mike-d3v/slime-stuff/dock/Plug.stl

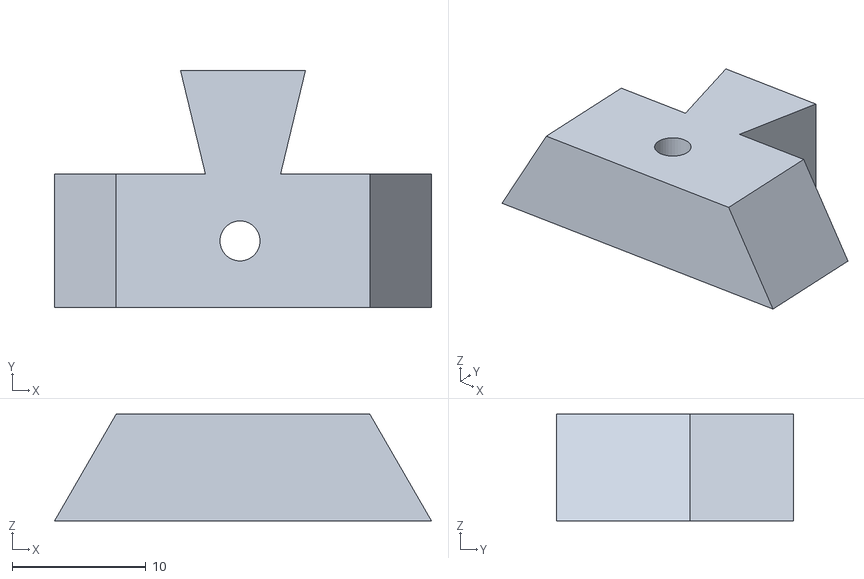
[picture p23: CAD file, 2022-05-23]
dock/Plug.stl
28.2 x 17.8 x 8.00
