mike-d3v/slime-stuff/buckles/secondary.stl

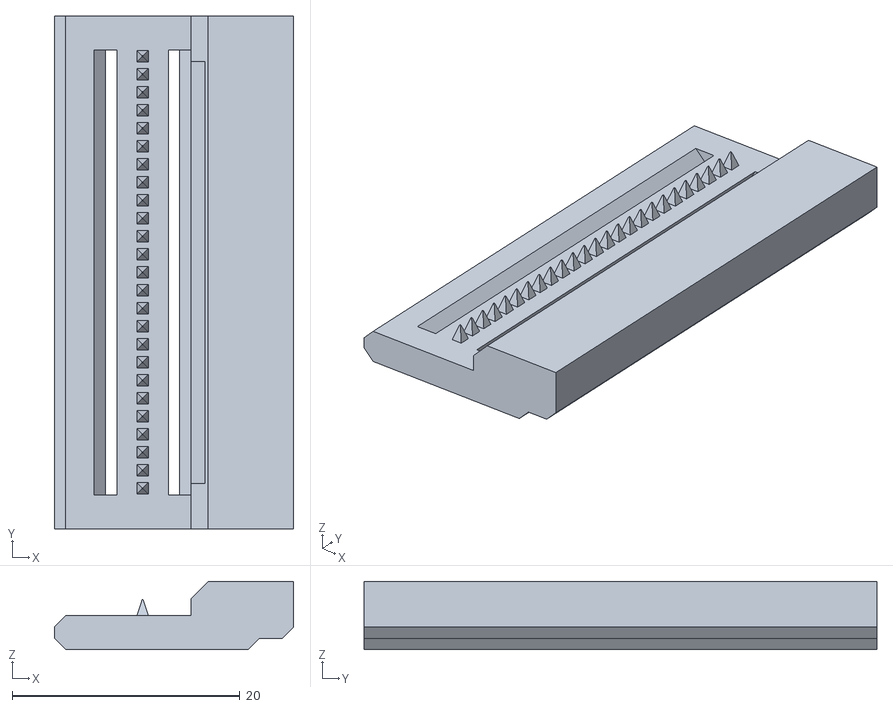
[picture p24: CAD file, 2022-05-23]
buckles/secondary.stl
21.0 x 45.0 x 6.00
