mike-d3v/slime-stuff/buckles/primaryExtension.stl

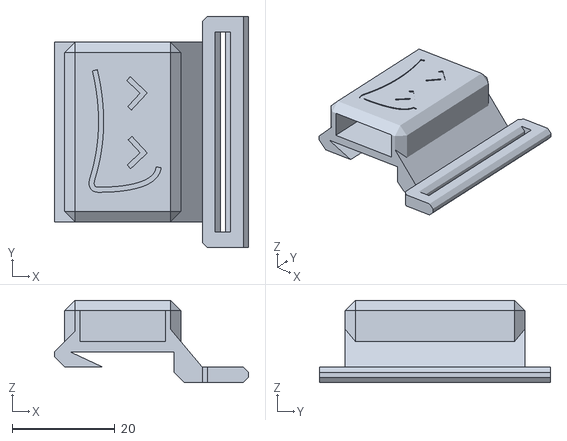
[picture p25: CAD file, 2022-05-23]
buckles/primaryExtension.stl
37.8 x 45.0 x 16.0
