mike-d3v/slime-stuff/buckles/extensionCap.stl

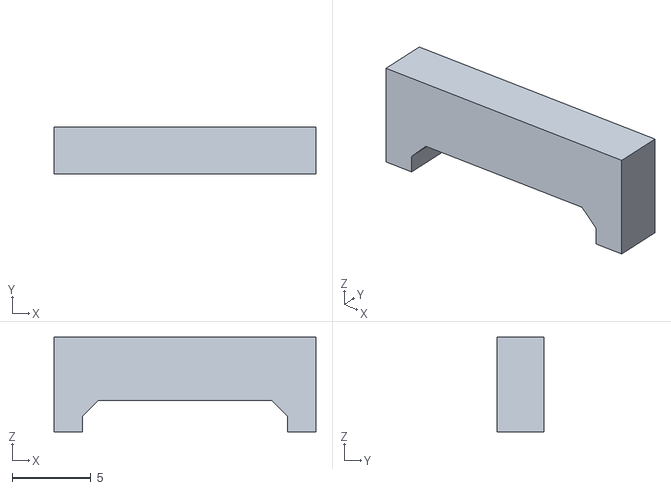
[picture p26: CAD file, 2022-05-23]
buckles/extensionCap.stl
16.6 x 3.00 x 6.00
