mike-d3v/slime-stuff/buckles/primary.stl

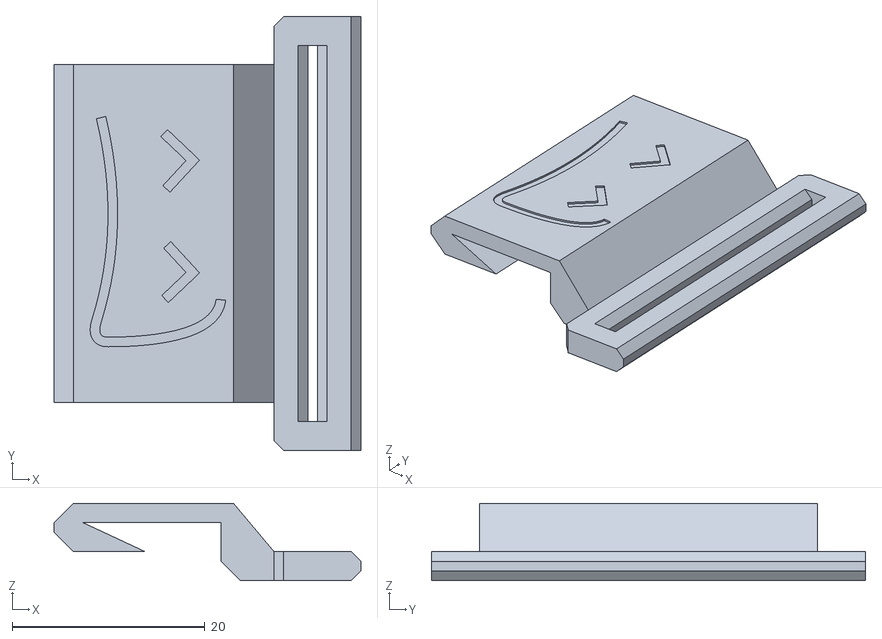
[picture p27: CAD file, 2022-05-23]
buckles/primary.stl
31.8 x 45.0 x 8.00
