mike-d3v/slime-stuff/buckles/secondary0.5mm.stl

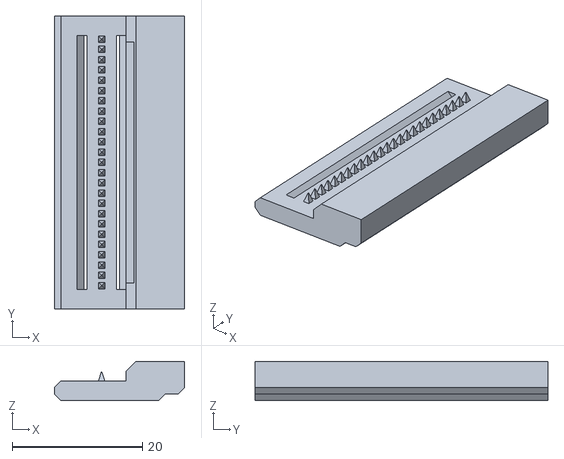
[picture p28: CAD file, 2022-05-23]
buckles/secondary0.5mm.stl
20.0 x 45.0 x 6.00
